haldarsaurav/desk_radar_esp32/docs/renders/looks/0_Original_stale.png

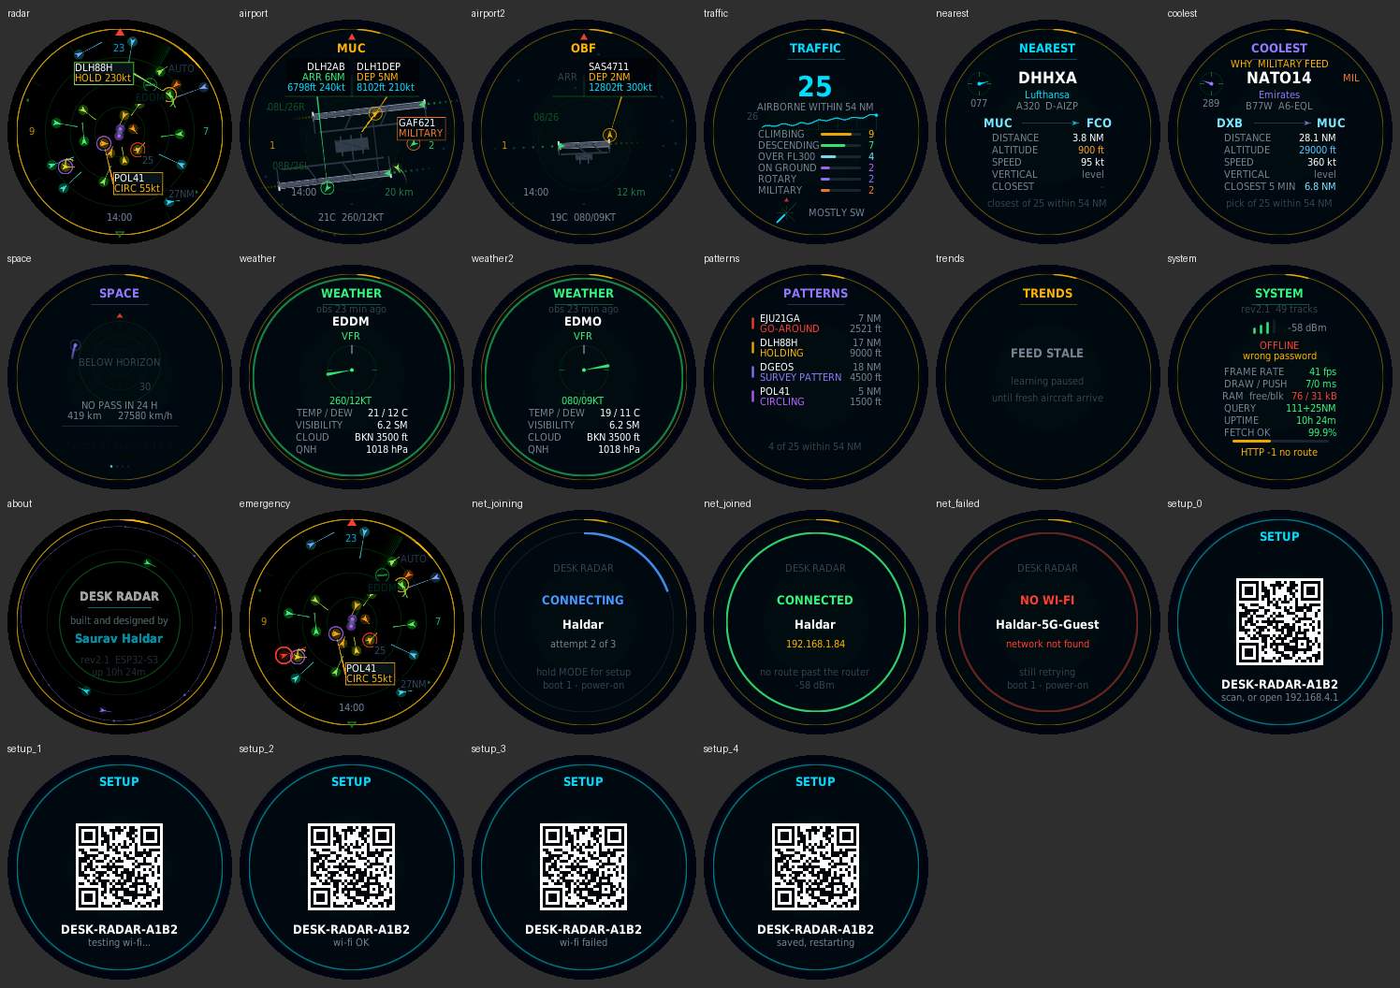
docs/renders/looks/0_Original_stale.png
