haldarsaurav/desk_radar_esp32/docs/renders/looks/1_Glass_Cockpit_empty.png

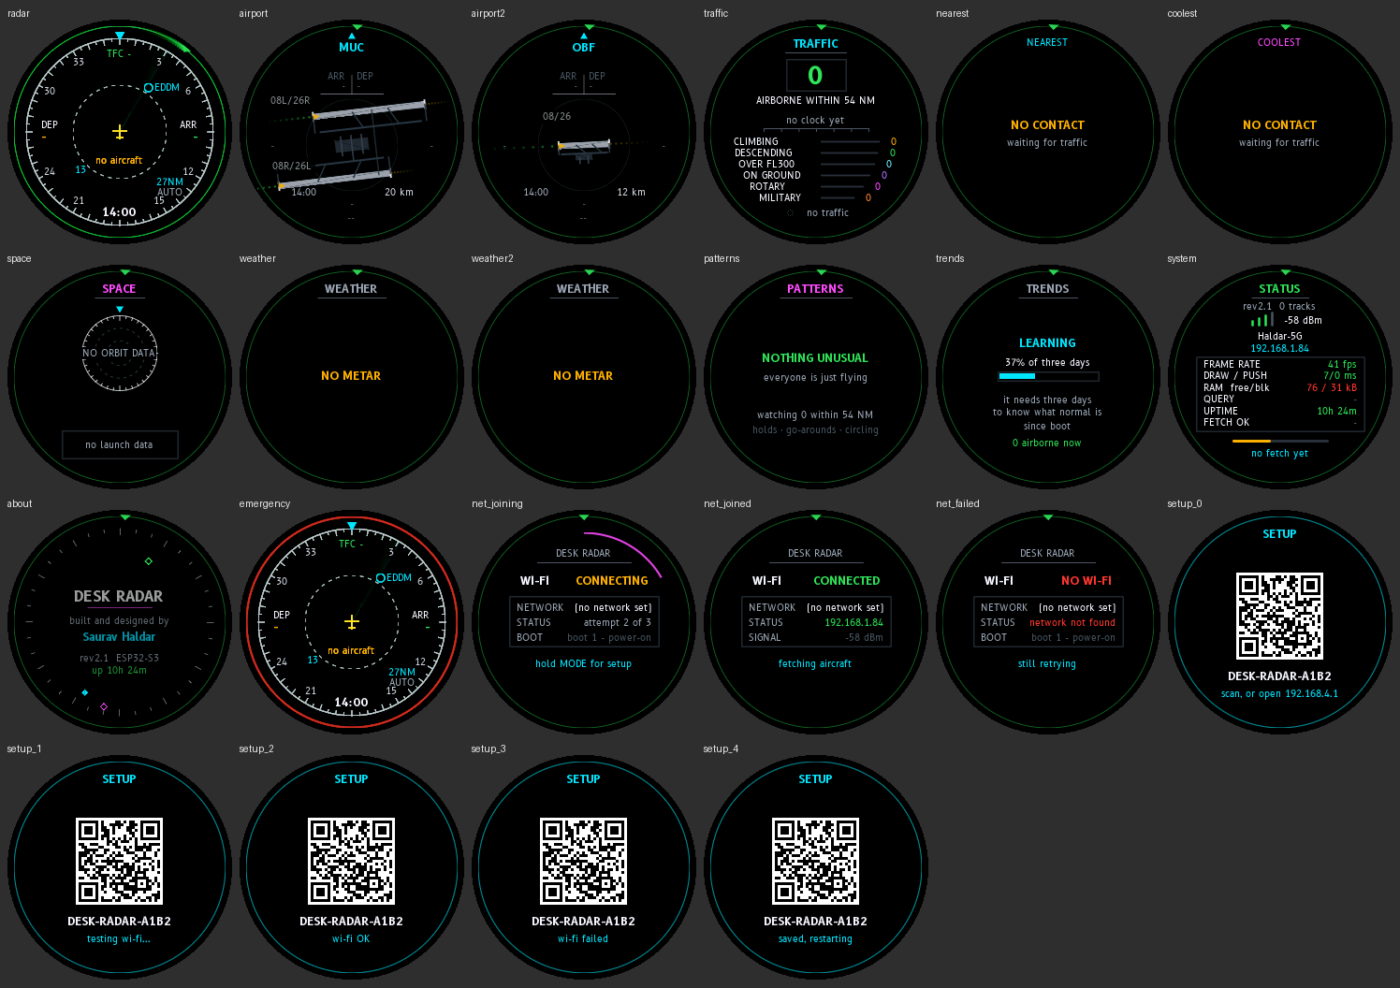
docs/renders/looks/1_Glass_Cockpit_empty.png
