haldarsaurav/desk_radar_esp32/docs/renders/looks/1_Glass_Cockpit_metric.png

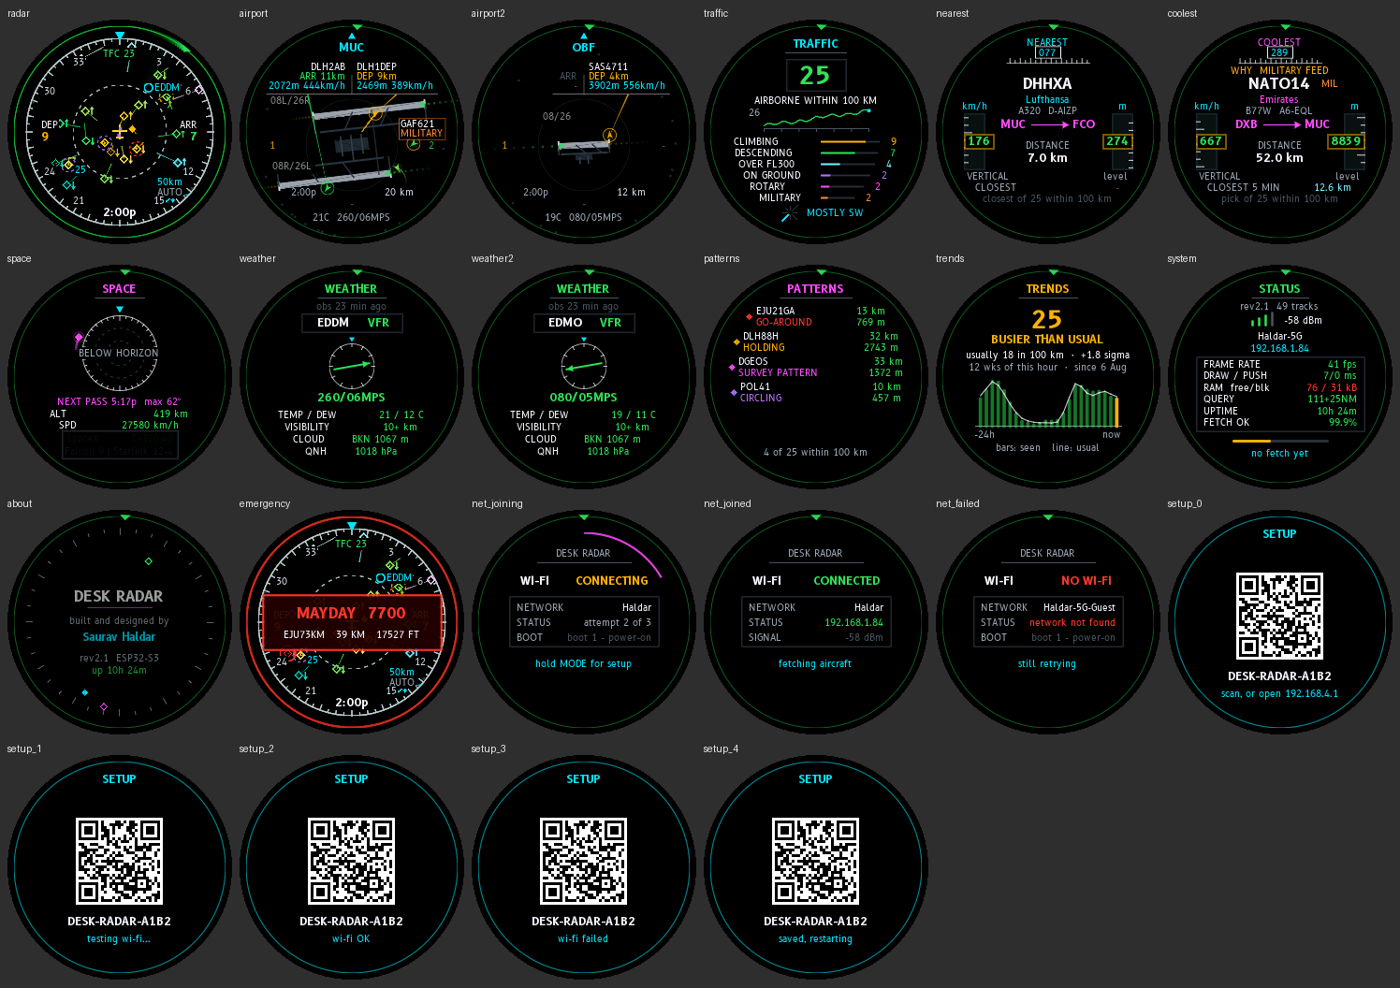
docs/renders/looks/1_Glass_Cockpit_metric.png
