haldarsaurav/desk_radar_esp32/docs/renders/looks/2_Chart_Paper_metric.png

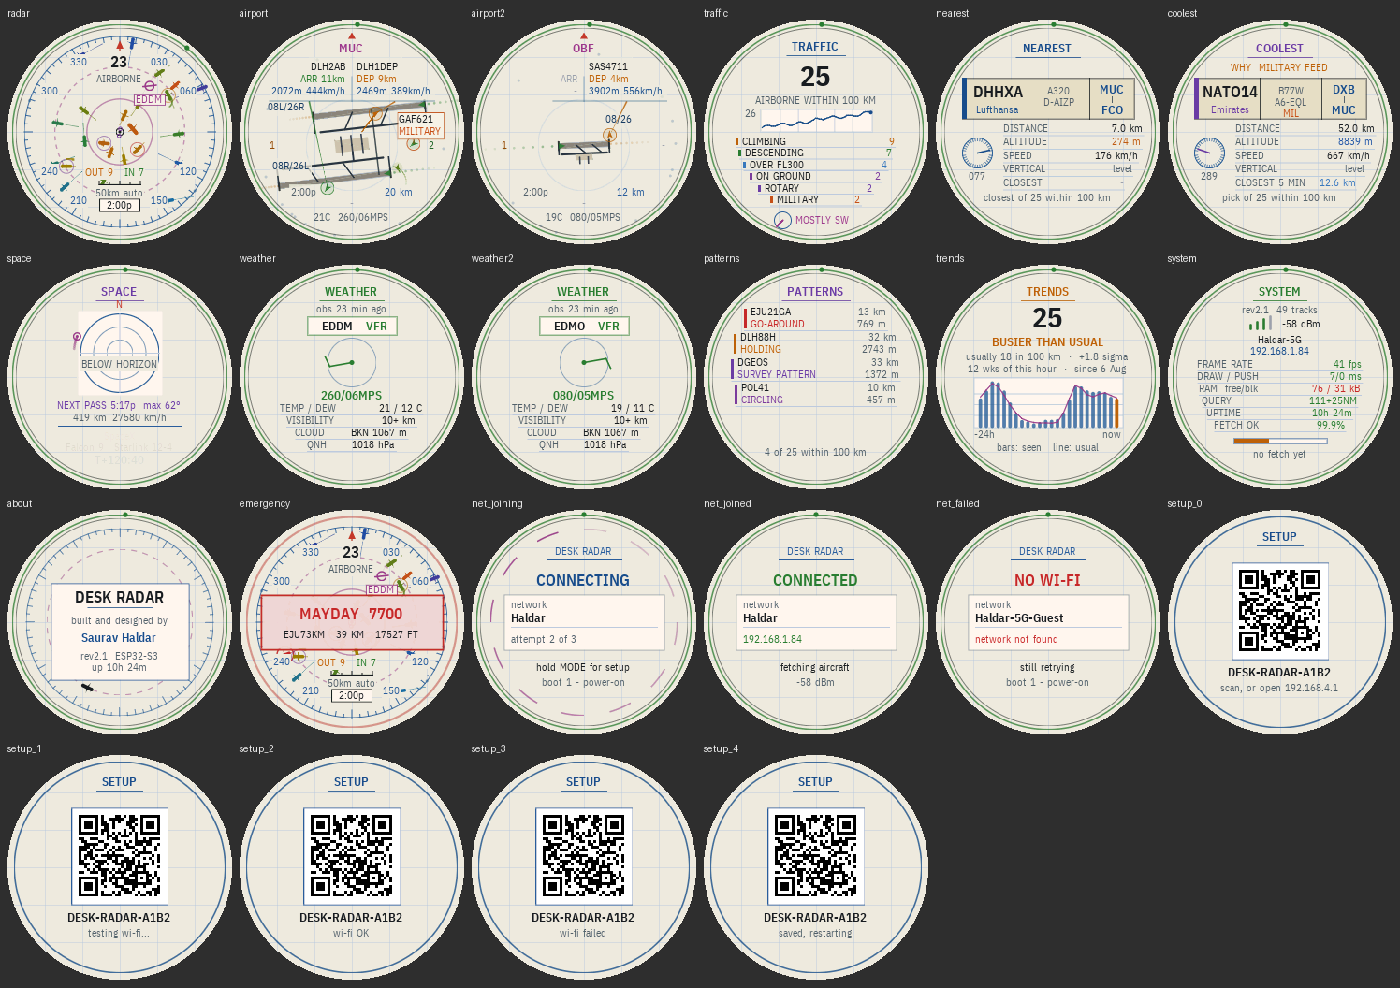
docs/renders/looks/2_Chart_Paper_metric.png
