haldarsaurav/desk_radar_esp32/docs/renders/looks/4_Night_Red_stale.png

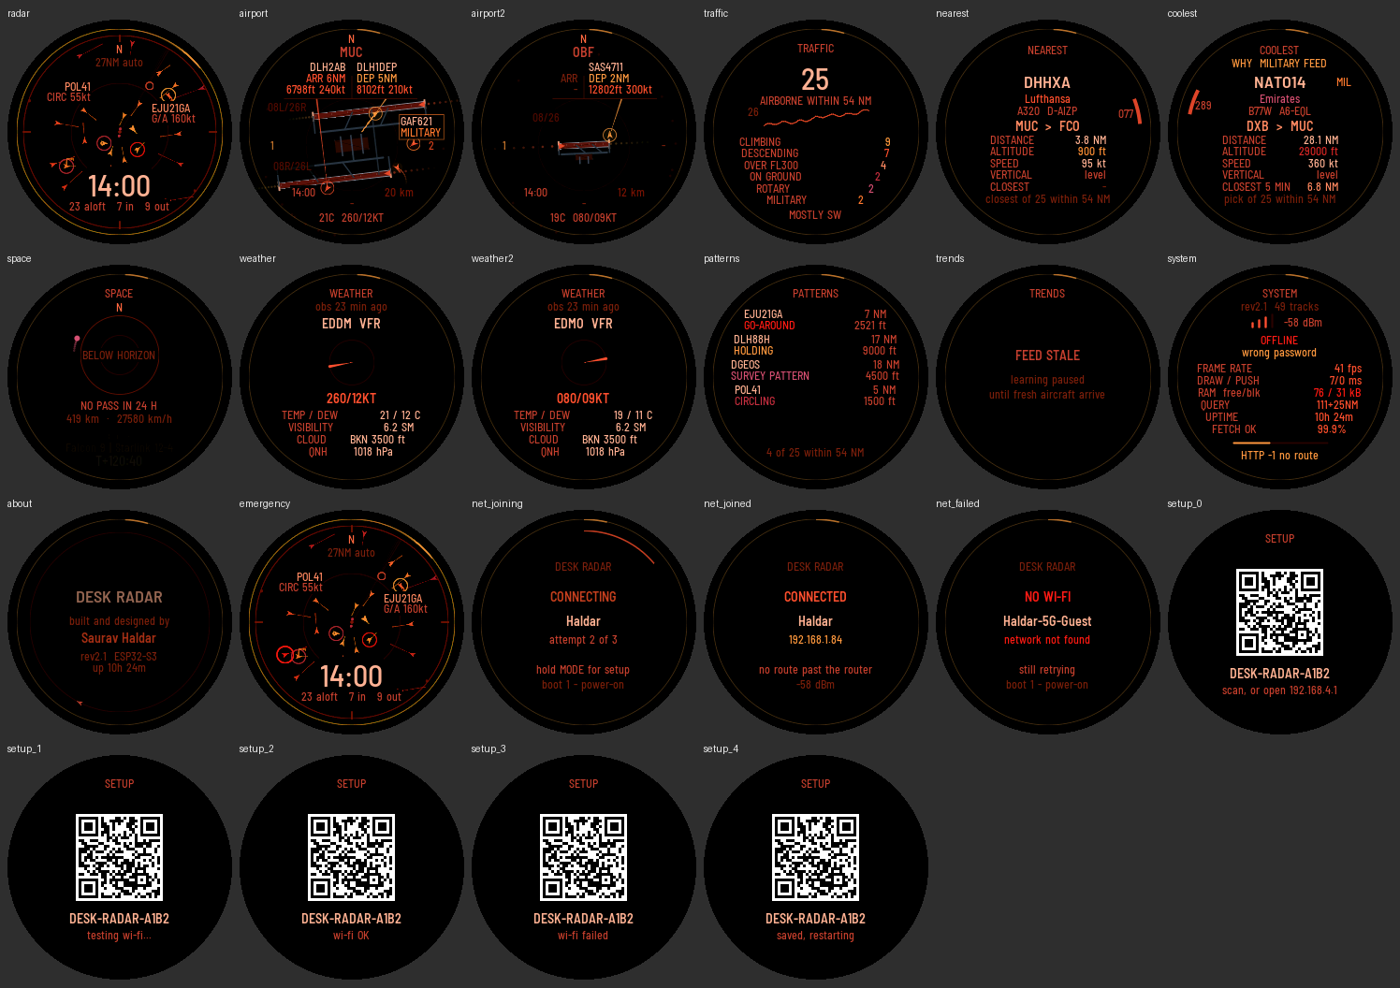
docs/renders/looks/4_Night_Red_stale.png
