haldarsaurav/desk_radar_esp32/docs/renders/looks/5_Steam_Gauge_metric.png

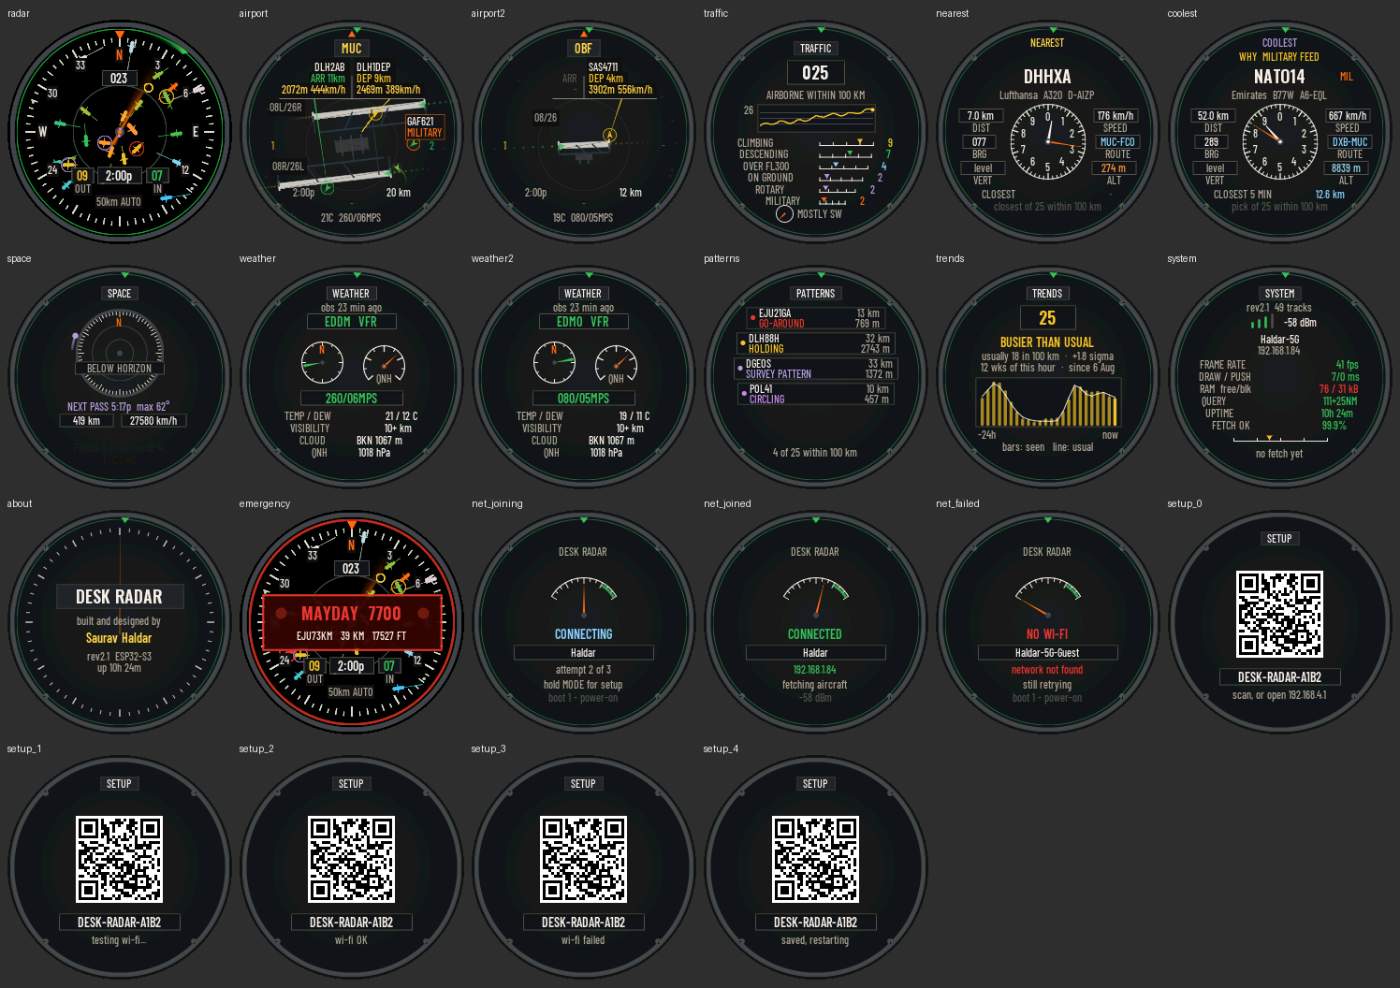
docs/renders/looks/5_Steam_Gauge_metric.png
